kaveeshwaragayanath/PomodoroTimer/WhatsApp Image 2023-09-04 at 13.59.55 (1).jpeg

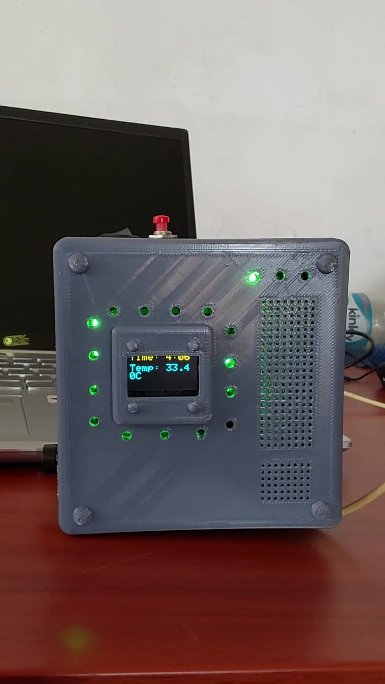
WhatsApp Image 2023-09-04 at 13.59.55 (1).jpeg
